fau-fablab/kassenautomat.mdb-interface/firmware/main.h

#include <avr/pgmspace.h>
void __attribute__((noreturn)) fatal_real(const char * PROGMEM str, uint8_t d);
#define FATAL(x) fatal_real(PSTR(x),0)
#define FATAL_h(x,d) fatal_real(PSTR(x),d)

#define TICKS_PER_S 5800 // how often is task_XYZ() called per milisecond
