fau-fablab/kassenautomat.mdb-interface/firmware/uart.h

/*
 *    Filename: lib/io/serial/uart.h
 *     Version: 0.0.1
 * Description: Beispieldatei
 *     License: GPLv2 or later
 *     Depends: io.h
 *
 *      Author: Copyright (C) Max Gaukler <development@maxgaukler.de> and additional Features by Philipp Hörauf
 *        Date: 2007-12-12
 *
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
 */
#ifndef _HAVE_LIB_IO_SERIAL_UART_H
#define _HAVE_LIB_IO_SERIAL_UART_H

#ifndef PE0
#define PE0 UPE0
#endif

#ifndef PE1
#define PE1 UPE1
#endif

#include "./io.h"
#include <avr/pgmspace.h>

void uartPC_init(void);
void uartPC_tx_blocking(unsigned char byte);
uint8_t uartPC_tx_ready(void);
void uartPC_tx(uint8_t byte);
uint8_t uartPC_rx(void);
void uartPC_tx_str(unsigned char* string);
uint8_t uartPC_rx_ready(void);
void uartBus_init(void);
uint8_t uartBus_tx_ready(void);
void uartBus_tx(uint8_t byte, uint8_t bit8);
uint16_t uartBus_rx(void);
void uartBus_tx_str(unsigned char* string);
uint8_t uartBus_rx_ready(void);


// UBRR=(F_CPU)/(baud*16L), aber gerundet:
// UBRR=(obere Formel*2 +1)/2

void uartPC_init() {
	uint16_t _ubrr=38; // 38400 @ 12MHz mit U2X=1
	uint8_t rx=1;
	uint8_t tx=1;
	// baud
	UBRR1H = _ubrr>>8;
	UBRR1L = _ubrr;
	
	
	// RX/TX aktivieren
	UCSR1A = (1<<U2X0);
	
	UCSR1B = (rx << RXEN1)|(tx << TXEN1);
	
	// 8 Bit Daten; 1 Stopbit; Synchronous Operation
	UCSR1C = (0 << USBS1) | (1 << UCSZ11) | (3 << UCSZ10);
}

void uartPC_tx_blocking(unsigned char byte) {
	while (!(UCSR1A & (1 << UDRE1))) {} // noch etwas blockiered
	UDR1=byte;
}

uint8_t uartPC_tx_ready(void) {
	return (UCSR1A & (1 << UDRE1));
}
void uartPC_tx(uint8_t byte) {
	if (!uartPC_tx_ready()) {
		FATAL("!uartPC_tx_ready");
	}
	UDR1=byte;
}

uint8_t uartPC_rx(void) {
//	while (!(UCSRA & (1 << RXC))) {} es wird nicht gewartet! kein delay erlaubt!
	return UDR1;
}

void uartPC_tx_str(unsigned char* string) {
	uint16_t i=0;
	while (string[i] != 0x00) {
		uartPC_tx_blocking(string[i]);	
		i++;
	}
}

void uartPC_tx_pstr(const char* PROGMEM str) {
	uint8_t byte;
	while ((byte=pgm_read_byte(str++))) {
		uartPC_tx_blocking(byte);
	}
}


uint8_t uartPC_rx_ready(void) {
	if (UCSR1A & (1<<RXC1)) {
		if (UCSR1A & (1<<PE1)) {
// 			Parity Error stillschweigend verwerfen
// 			volatile uint8_t tmp=UDR;
// 			tmp++;
			return 0;
		} else {
			return 1;
		}
	} else {
		return 0;
	}
}


void uartBus_init(void) {
	uint16_t _ubrr=77; // 9600 @ 12MHz
	// baud
	UBRR0H = _ubrr>>8;
	UBRR0L = _ubrr;
	
	// RX/TX aktivieren
	UCSR0B = (1 << RXEN0)|(1 << TXEN0) | (1 << UCSZ02);
	
	// 9 Bit Daten; 2 Stopbits; Synchronous Operation
	UCSR0C = (1<<USBS0) |  (1 << UCSZ01) | (3 << UCSZ00);
}

uint8_t uartBus_tx_ready(void) {
	return (UCSR0A & (1 << UDRE0));
}
void uartBus_tx(uint8_t byte, uint8_t bit8) {
	if (!uartBus_tx_ready()) {
		FATAL("!uartBus_tx_ready");
	}
	UCSR0B &= ~(1<<TXB80);
	if (bit8) {
		UCSR0B |= (1<<TXB80);
	}
	UDR0=byte;
}

uint16_t uartBus_rx(void) {
//	while (!(UCSRA & (1 << RXC))) {} es wird nicht gewartet! kein delay erlaubt!
	//volatile uint8_t status=UCSR1A;
	volatile uint8_t bit8=!!(UCSR0B&(1<<RXB80));
	return UDR0 | (bit8<<8);
}

// void uartBus_tx_str(unsigned char* string) {
// 	uint16_t i=0;
// 	while (string[i] != 0x00) {
// 		uartBus_tx_blocking(string[i]);	
// 		i++;
// 	}
// }

uint8_t uartBus_rx_ready(void) {
	if (UCSR0A & (1<<RXC0)) {
		if (UCSR0A & (1<<PE0)) {
// 			Parity Error stillschweigend verwerfen
// 			volatile uint8_t tmp=UDR;
// 			tmp++;
			return 0;
		} else {
			return 1;
		}
	} else {
		return 0;
	}
}

#endif
